geertpeeters/Epiphone-BC30/schematics/gain-stage.kicad_sch

## KiCad design schematics/gain-stage.kicad_sch (2026-09-13)

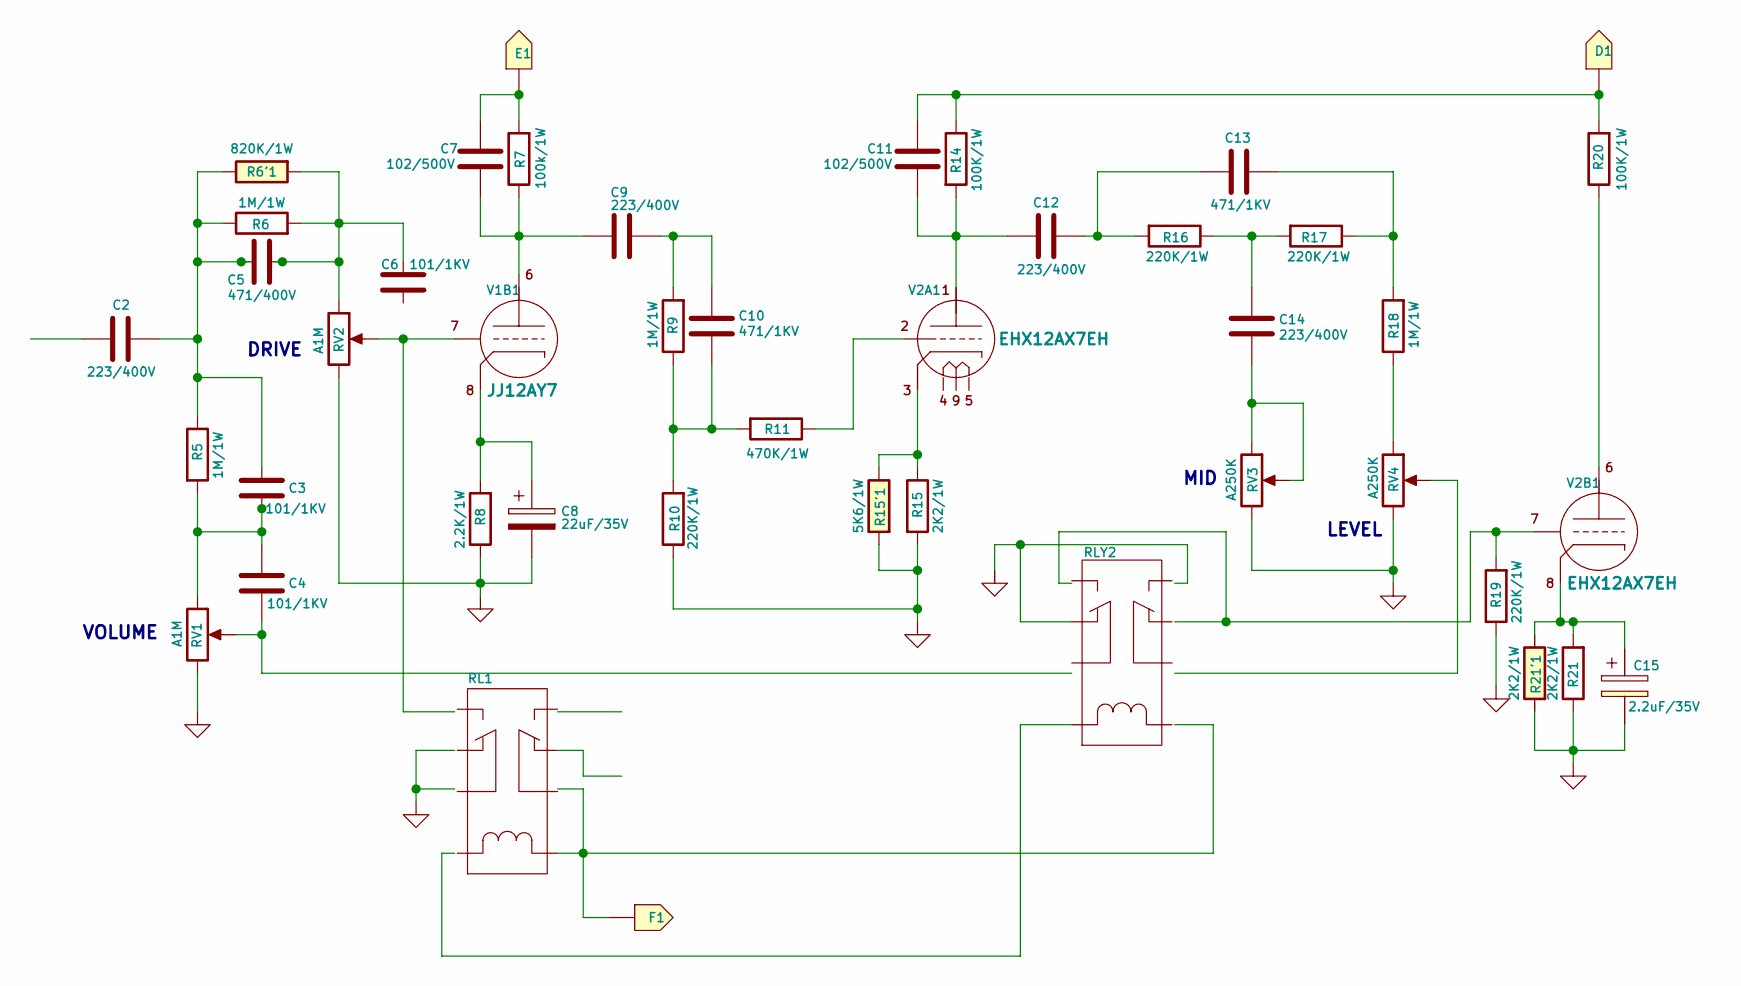
[picture p6: schematic gain-stage.kicad_sch]

Parts:
C2, C9, C12, C14: 223/400V
C3, C4, C6: 101/1KV
C5: 471/400V
C7, C11: 102/500V
C8: 22uF/35V
C10, C13: 471/1KV
C15: 2.2uF/35V
D1: (no value)
E1: (no value)
F1: (no value)
R5, R6, R9, R18: 1M/1W
R6'1: 820K/1W
R7: 100k/1W
R8: 2.2K/1W
R10, R16, R17, R19: 220K/1W
R11: 470K/1W
R14, R20: 100K/1W
R15, R21, R21'1: 2K2/1W
R15'1: 5K6/1W
RL1: (no value)
RLY2: (no value)
RV1, RV2: A1M
RV3, RV4: A250K
V1B1: JJ12AY7
V2A1, V2B1: EHX12AX7EH

Connections:
GND: C8.2, C15.2, R8.1, R10.1, R15.2, R15'1.1, R19.1, R21.1, R21'1.1, RLY2., RV1., RV2., RV3., RV4.
unnamed: C2.2, C3.1, C5.1, R5.1, R6.1, R6'1.2
unnamed: C3.2, C4.1, R5.2, RV1.
unnamed: C4.2, RV1.
unnamed: C5.2, C6.1, R6.2, R6'1.1, RV2.
unnamed: C7.1, E1., R7.2
unnamed: C7.2, C9.1, R7.1, V1B1.
unnamed: C8.1, R8.2, V1B1.
unnamed: C9.2, C10.1, R9.2
unnamed: C10.2, R9.1, R10.2, R11.2
unnamed: C11.1, C12.1, R14.2, V2A1.
unnamed: C11.2, D1., R14.1, R20.2
unnamed: C12.2, C13.2, R16.2
unnamed: C13.1, R17.1, R18.2
unnamed: C14.1, R16.1, R17.2
unnamed: C14.2, RV3.
unnamed: C15.1, R21.2, R21'1.2, V2B1.
unnamed: F1., RL1.
unnamed: R11.1, V2A1.
unnamed: R15.1, R15'1.2, V2A1.
unnamed: R18.1, RV4.
unnamed: R19.2, V2B1.
unnamed: R20.1, V2B1.
unnamed: RV2., V1B1.

Notes on the sheet:
MID
DRIVE
VOLUME
LEVEL
