geertpeeters/Epiphone-BC30/schematics/phase-inverter.kicad_sch

## KiCad design schematics/phase-inverter.kicad_sch (2026-04-12)

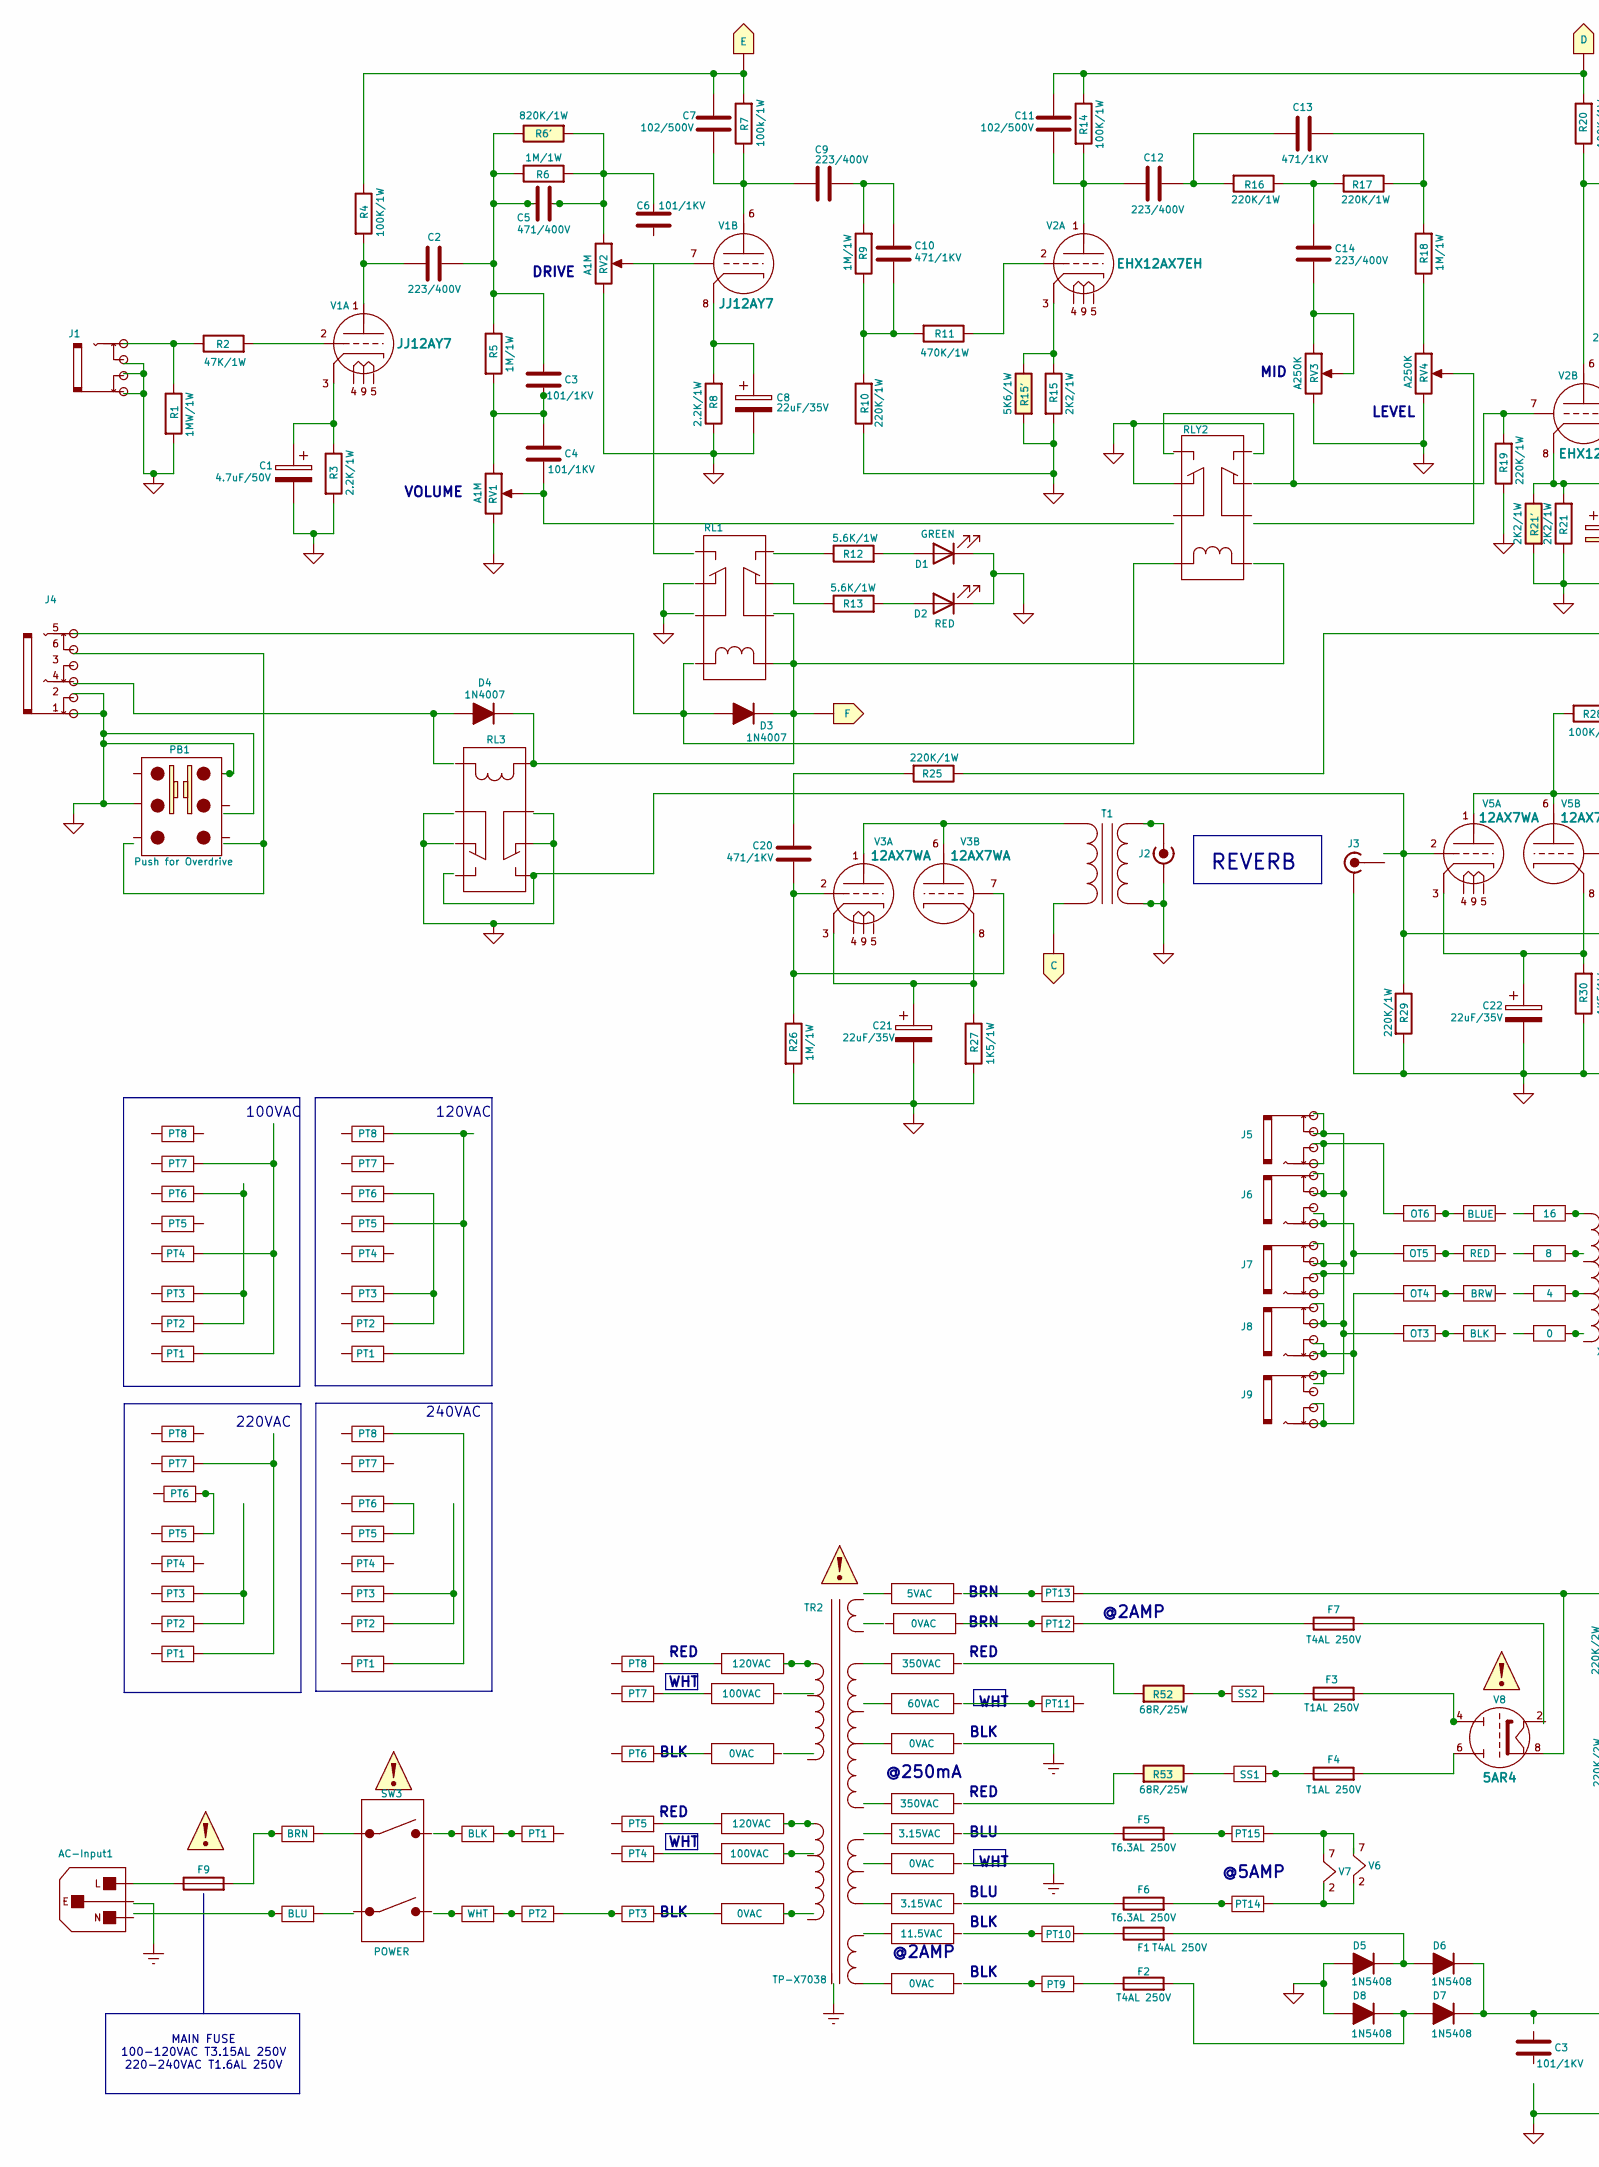
[picture p7: schematic phase-inverter.kicad_sch, part in row 1, column 1]

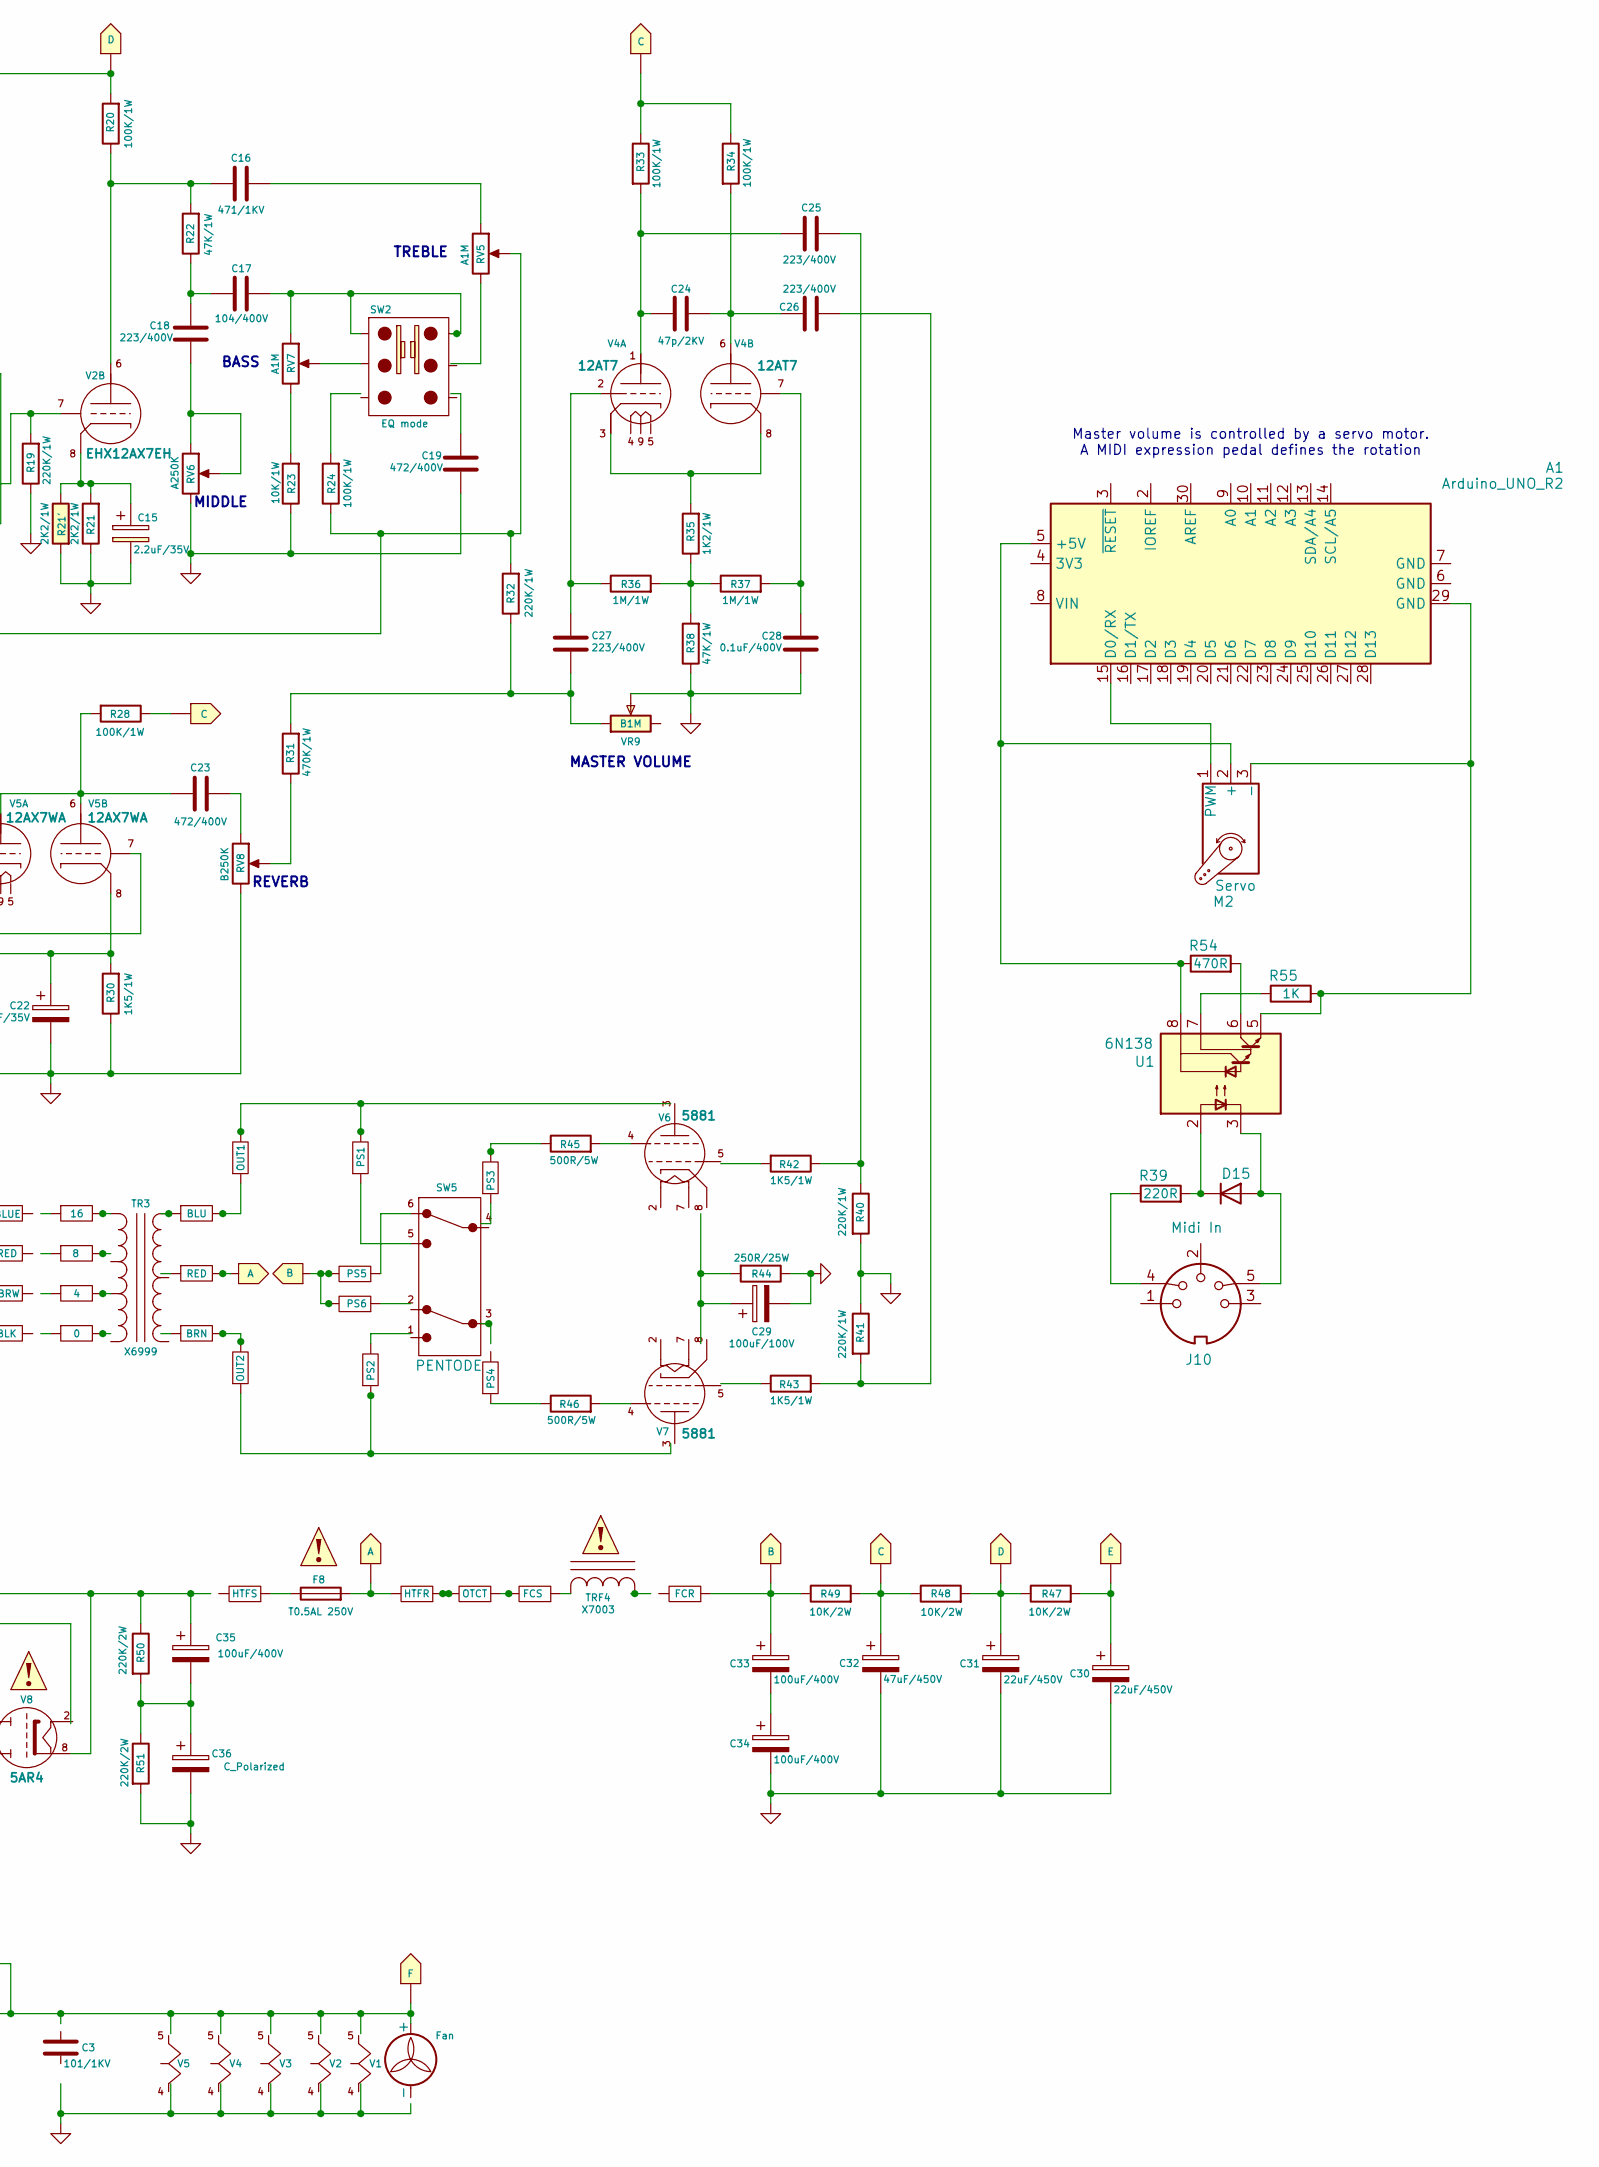
[picture p8: schematic phase-inverter.kicad_sch, part in row 1, column 2]

Parts:
0VAC, 3.15VAC, 5VAC, 11.5VAC, 60VAC, 100VAC, 120VAC, 350VAC: (no value)
A: (no value)
A1: Arduino_UNO_R2
AC-Input1: (no value)
B: (no value)
BLK: (no value)
BLU: (no value)
BLUE: (no value)
BRN: (no value)
C: (no value)
C1: 4.7uF/50V
C2, C9, C12, C14, C18, C25, C26, C27: 223/400V
C3, C4, C6: 101/1KV
C5: 471/400V
C7, C11: 102/500V
C8, C21, C22: 22uF/35V
C10, C13, C16, C20: 471/1KV
C15: 2.2uF/35V
C17: 104/400V
C19, C23: 472/400V
C24: 47p/2KV
C28: 0.1uF/400V
C29: 100uF/100V
C30, C31: 22uF/450V
C32: 47uF/450V
C33, C34, C35: 100uF/400V
C36: C_Polarized
D, D9, D10, D11, D12, D13, D14: (no value)
D1: GREEN
D2: RED
D3, D4: 1N4007
D5, D6, D7, D8: 1N5408
D15: D
E: (no value)
F: (no value)
F1, F2, F7: T4AL 250V
F3, F4: T1AL 250V
F5, F6: T6.3AL 250V
F8: T0.5AL 250V
F9: Fuse
FCR: (no value)
FCS: (no value)
HTFR: (no value)
HTFS: (no value)
J1, J2, J4, J5, J6, J7, J8, J9: (no value)
J3: Conn_Coaxial_Power
J10: Midi In
M1: Fan
M2: Servo
OT6: OT6
OTCT: (no value)
OUT1, OUT2: (no value)
PB1: Push for Overdrive
PS1, PS2, PS3, PS4, PS5, PS6: (no value)
PT1, PT2, PT3, PT4, PT5, PT6, PT7, PT8, PT9, PT10, PT11, PT12, PT13, PT14, PT15: (no value)
R1: 1MW/1W
R2, R22, R38: 47K/1W
R3, R8: 2.2K/1W
R4, R14, R20, R24, R28, R33, R34: 100K/1W
R5, R6, R9, R18, R26, R36, R37: 1M/1W
R6': 820K/1W
R7: 100k/1W
R10, R16, R17, R19, R25, R29, R32, R40, R41: 220K/1W
R11, R31: 470K/1W
R12, R13: 5.6K/1W
R15, R21, R21': 2K2/1W
R15': 5K6/1W
R23: 10K/1W
R27, R30, R42, R43: 1K5/1W
R35: 1K2/1W
R39: 220R
R44: 250R/25W
R45, R46: 500R/5W
R47, R48, R49: 10K/2W
R50, R51: 220K/2W
R52, R53: 68R/25W
R54: 470R
R55: 1K
RL1, RL3: (no value)
RLY2: (no value)
RV1, RV2, RV5, RV7: A1M
RV3, RV4, RV6: A250K
RV8: B250K
SS1, SS2: (no value)
SW2: EQ mode
SW3: POWER
SW5: PENTODE
T1: (no value)
TR2: TP-X7038
TR3: X6999
TRF4: X7003
U1: 6N138
V1, V2, V3, V4, V5: (no value)
V1A, V1B: JJ12AY7
V2A, V2B: EHX12AX7EH
V3A, V3B, V5A, V5B: 12AX7WA
V4A, V4B: 12AT7
V6, V7: 5881
V8: 5AR4
VR9: B1M
WHT: (no value)
a: 0
d: OT3
f: OT4
ff: 16
s: 4

Connections:
GND: C1.2, C8.2, C15.2, C19.1, C21.2, C22.2, C28.2, C29.2, C30.2, C31.2, C32.2, C34.2, C36.2, D1.1 (K), D2.1 (K), D5.2 (A), D8.2 (A), J2., J3., J4., PB1., R1.2, R3.2, R8.1, R10.1, R15.2, R15'.1, R19.1, R21.1, R21'.1, R23.1, R26.2, R27.2, R29.2, R30.1, R38.1, R40.2, R41.1, R44.1, R51.2, RL3., RLY2., RV1., RV2., RV3., RV4., RV6., RV8., T1., VR9.
unnamed: 0VAC., PT3., PT6., PT12., TR2.
unnamed: 3.15VAC., TR2.
unnamed: 100VAC., PT4., PT7.
unnamed: 120VAC., PT5., PT8., TR2.
unnamed: 350VAC., TR2.
unnamed: A1.5 (+5V), M2.2 (+), R54.1, U1.8 (VCC)
unnamed: A1.15 (D0/RX), M2.1 (PWM)
unnamed: A1.29 (GND), M2.3 (-), R55.2, U1.5 (GND)
unnamed: A., F8.2, HTFR., d.
unnamed: AC-Input1., F9.1
unnamed: B., C33.1, FCR., PS5., PS6., R49.1
unnamed: BLK., PT1.
unnamed: BLUE., OT6.
unnamed: BRN., F9.2, SW3.
unnamed: C1.1, R3.1, V1A.
unnamed: C2.1, R4.2, V1A.
unnamed: C2.2, C3.1, C5.1, R5.1, R6.1, R6'.2
unnamed: C3.2, C4.1, R5.2, RV1.
unnamed: C4.2, RV1.
unnamed: C5.2, C6.1, R6.2, R6'.1, RV2.
unnamed: C7.1, E., R4.1, R7.2
unnamed: C7.2, C9.1, R7.1, V1B.
unnamed: C8.1, R8.2, V1B.
unnamed: C9.2, C10.1, R9.2
unnamed: C10.2, R9.1, R10.2, R11.2
unnamed: C11.1, C12.1, R14.2, V2A.
unnamed: C11.2, D., R14.1, R20.2
unnamed: C12.2, C13.2, R16.2
unnamed: C13.1, R17.1, R18.2
unnamed: C14.1, R16.1, R17.2
unnamed: C14.2, RV3.
unnamed: C15.1, R21.2, R21'.2, V2B.
unnamed: C16.1, R20.1, R22.2, V2B.
unnamed: C16.2, RV5.
unnamed: C17.1, C18.2, R22.1
unnamed: C17.2, RV7., SW2.
unnamed: C18.1, RV6.
unnamed: C20.1, R25.2
unnamed: C20.2, R26.1, V3A., V3B.
unnamed: C21.1, R27.1, V3A., V3B.
unnamed: C22.1, R30.2, V5A., V5B.
unnamed: C23.1, R28.2, V5A., V5B.
unnamed: C23.2, RV8.
unnamed: C24.1, C26.2, R34.2, V4B.
unnamed: C24.2, C25.2, R33.2, V4A.
unnamed: C25.1, R40.1, R42.1
unnamed: C26.1, R41.2, R43.2
unnamed: C27.1, R36.1, V4A.
unnamed: C27.2, R31.2, R32.1, VR9.
unnamed: C28.1, R37.2, V4B.
unnamed: C29.1, R44.2
unnamed: C30.1, E., R47.2
unnamed: C31.1, D., R47.1, R48.2
unnamed: C33.2, C34.1
unnamed: C35.1, PT13., R50.1, V8.
unnamed: C35.2, C36.1, R50.2, R51.1
unnamed: C., C32.1, R28.1, R33.1, R34.1, R48.1, R49.2, T1.
unnamed: D1.2 (A), R12.2
unnamed: D2.2 (A), R13.2
unnamed: D3.1 (K), D4.1 (K), F., RL1., RL3.
unnamed: D3.2 (A), J4., RLY2.
unnamed: D5.1 (K), D6.2 (A), F1.2
unnamed: D6.1 (K), D7.1 (K), F., M1.
unnamed: D7.2 (A), D8.1 (K), F2.2
unnamed: D15.1 (K), R39.2, U1.2 (C1)
unnamed: D15.2 (A), J10.5, U1.3 (C2)
unnamed: F1.1, PT10.
unnamed: F2.1, PT9.
unnamed: F3.1, SS2.
unnamed: F3.2, V8.
unnamed: F4.1, SS1.
unnamed: F4.2, V8.
unnamed: F5.2, PT15.
unnamed: F6.2, PT14.
unnamed: F7.1, PT12.
unnamed: F8.1, HTFS.
unnamed: FCS., OTCT., TRF4.
unnamed: HTFR., OTCT.
unnamed: J1., R1.1, R2.1
unnamed: J2., T1.
unnamed: J5., OT6.
unnamed: J6., J7., a.
unnamed: J8., d.
unnamed: J9., f.
unnamed: J10.4, R39.1
unnamed: OUT1., PS1.
unnamed: OUT2., PS2., a.
unnamed: PS1., SW5.
unnamed: PS3., R45.1
unnamed: PS4., R46.1
unnamed: PS5., SW5.
unnamed: PT1., PT4., PT5., PT7., PT8.
unnamed: PT2., PT3., PT6., WHT.
unnamed: PT5., PT6.
unnamed: PT14., V6.
unnamed: PT15., V7.
unnamed: R2.2, V1A.
unnamed: R11.1, V2A.
unnamed: R13.1, RL1.
unnamed: R15.1, R15'.2, V2A.
unnamed: R18.1, RV4.
unnamed: R19.2, V2B.
unnamed: R23.2, RV7.
unnamed: R24.1, R25.1, R32.2, RV5.
unnamed: R29.1, RL3., V5A., V5B.
unnamed: R31.1, RV8.
unnamed: R35.1, R36.2, R37.1, R38.2
unnamed: R35.2, V4A., V4B.
unnamed: R45.2, V6.
unnamed: R46.2, V7.
unnamed: R52.2, SS2.
unnamed: R53.2, SS1.
unnamed: R54.2, U1.6 (VO2)
unnamed: R55.1, U1.7 (VO1)
unnamed: RV2., V1B.
unnamed: RV7., SW2.
unnamed: T1., V3A., V3B.
unnamed: TR3., ff., s.
unnamed: a., s.
unnamed: d., f.

Notes on the sheet:
TREBLE
MID
RED
BRN
DRIVE
BLK
MIDDLE
Master volume is controlled by a servo motor. A MIDI expression pedal defines the rotation
MAIN FUSE 100-120VAC T3.15AL 250V 220-240VAC T1.6AL 250V
@2AMP
220VAC
WHT
100VAC
120VAC
MASTER VOLUME
240VAC
VOLUME
BLU
REVERB
BASS
@250mA
@5AMP
LEVEL
