geertpeeters/Epiphone-BC30/schematics/servo-controlled-master-volume.kicad_sch

## KiCad design schematics/servo-controlled-master-volume.kicad_sch (2026-09-13, an earlier design)

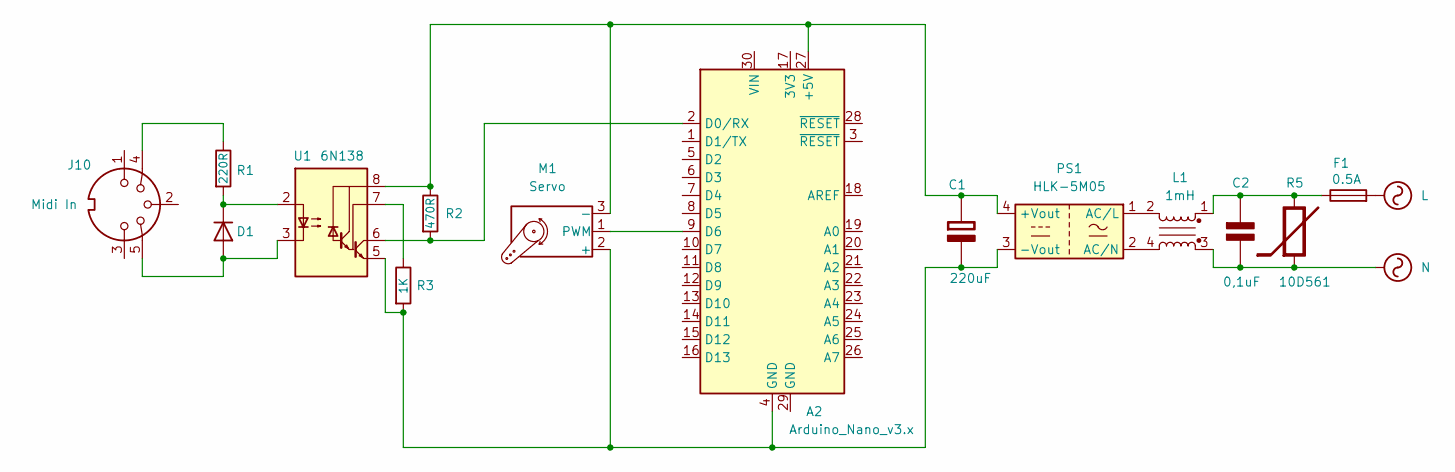
[picture p9: schematic servo-controlled-master-volume.kicad_sch]

Parts:
A2: Arduino_Nano_v3.x; Arduino_Nano
C1: 220uF; Rating V
C2: 0,1uF; Rating V
D1: D
F1: 0.5A
J10: Midi In
L1: 1mH; Choke_Schaffner_RN102-04-14.0x14.0mm
M1: Servo
PS1: HLK-5M05; Converter_ACDC_Hi-Link_HLK-5Mxx
R1: 220R
R2: 470R
R3: 1K
R5: 10D561; Rating NTC
U1: 6N138

Connections:
L: F1.2
N: C2.2 (-), L1.3, R5.2 (-)
unnamed: A2.2 (D0/RX), R2.2, U1.6 (VO2)
unnamed: A2.4 (GND), C1.2 (-), M1.2 (+), PS1.3 (-Vout), R3.2, U1.5 (GND)
unnamed: A2.9 (D6), M1.1 (PWM)
unnamed: A2.27 (+5V), C1.1 (+), M1.3 (-), PS1.4 (+Vout), R2.1, U1.8 (VCC)
unnamed: C2.1 (+), F1.1, L1.1, R5.1 (+)
unnamed: D1.1 (K), R1.2, U1.2 (C1)
unnamed: D1.2 (A), J10.5, U1.3 (C2)
unnamed: J10.4, R1.1
unnamed: L1.2, PS1.1 (AC/L)
unnamed: L1.4, PS1.2 (AC/N)
unnamed: R3.1, U1.7 (VO1)
