geertpeeters/Epiphone-BC30/schematics/tone-stack.kicad_sch

## KiCad design schematics/tone-stack.kicad_sch (2026-09-13)

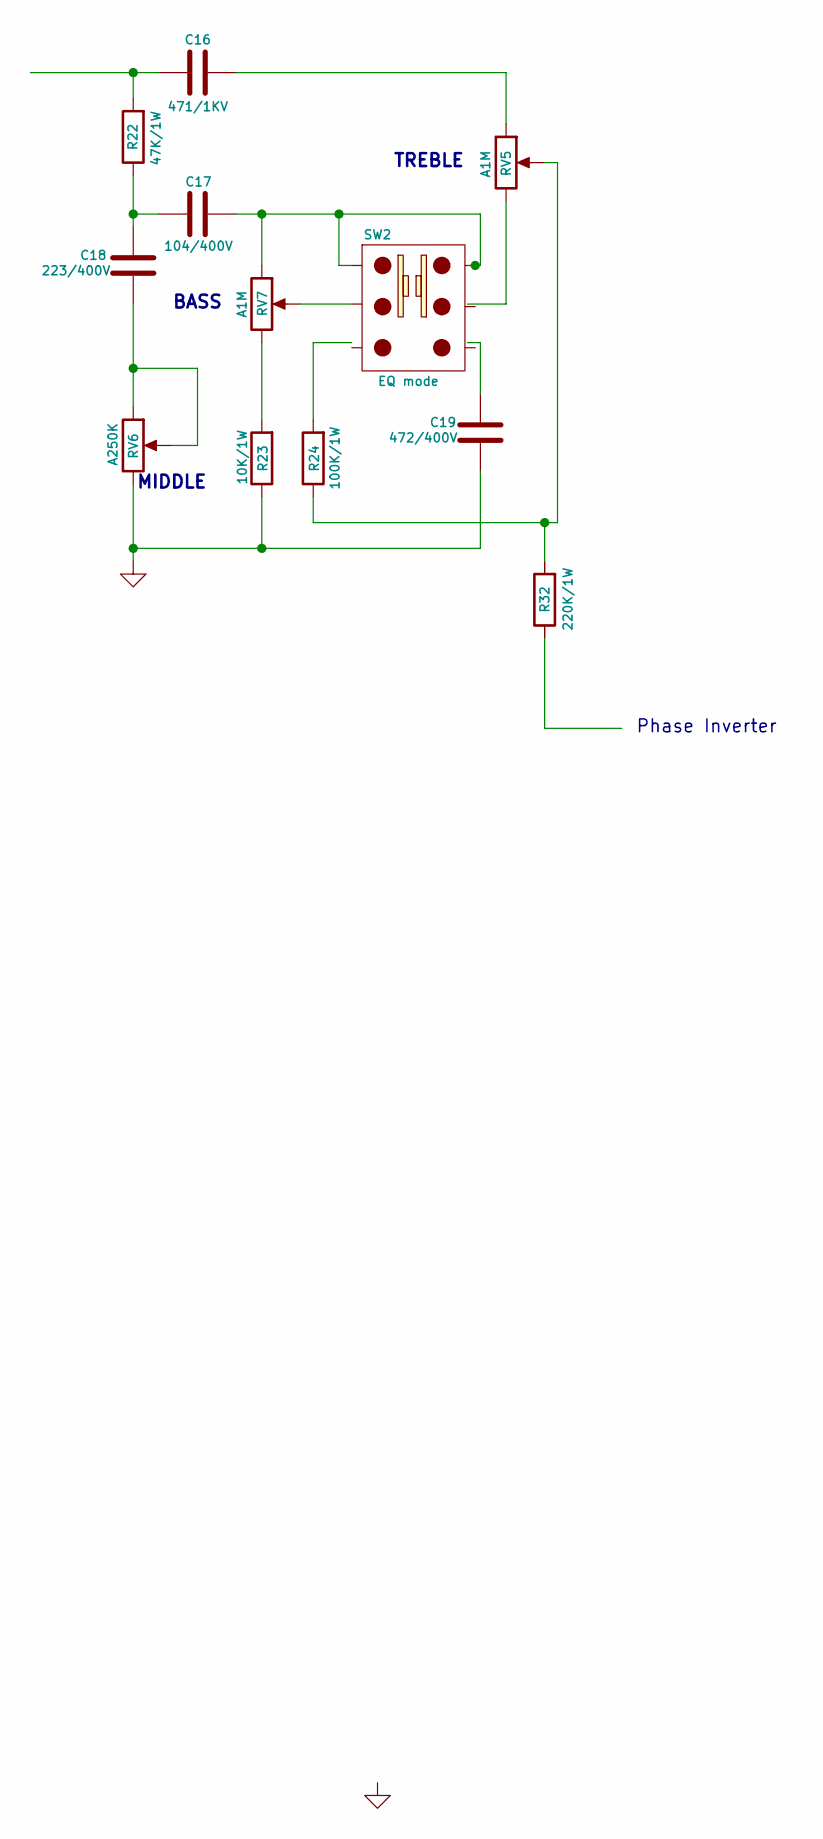
[picture p10: schematic tone-stack.kicad_sch]

Parts:
C16: 471/1KV
C17: 104/400V
C18: 223/400V
C19: 472/400V
R22: 47K/1W
R23: 10K/1W
R24: 100K/1W
R32: 220K/1W
RV5, RV7: A1M
RV6: A250K
SW2: EQ mode

Connections:
GND: C19.1, R23.1, RV6.
unnamed: C16.1, R22.2
unnamed: C16.2, RV5.
unnamed: C17.1, C18.2, R22.1
unnamed: C17.2, RV7., SW2.
unnamed: C18.1, RV6.
unnamed: R23.2, RV7.
unnamed: R24.1, R32.2, RV5.
unnamed: RV7., SW2.

Notes on the sheet:
Phase Inverter
TREBLE
MIDDLE
BASS
